punee995/OverWatch-485/SW/src/boards/RAK811BreakBoard/uart-board.h

/*
 / _____)             _              | |
( (____  _____ ____ _| |_ _____  ____| |__
 \____ \| ___ |    (_   _) ___ |/ ___)  _ \
 _____) ) ____| | | || |_| ____( (___| | | |
(______/|_____)_|_|_| \__)_____)\____)_| |_|
    (C)2016 Semtech

Description: Board UART driver implementation

License: Revised BSD License, see LICENSE.TXT file include in the project

Maintainer: Miguel Luis and Gregory Cristian
*/
#ifndef __UART_MCU_H__
#define __UART_MCU_H__

/*!
 * UART peripheral ID
 */
typedef enum
{
    UART_1,
		UART_3,
	  UART_COUNT,
    UART_USB_CDC = 255,
}UartId_t;


int e_getchar(void);
int m_printchar(char ch);
/*!
 * \brief Initializes the UART object and MCU peripheral
 *
 * \param [IN] obj  UART object
 * \param [IN] tx   UART Tx pin name to be used
 * \param [IN] rx   UART Rx pin name to be used
 */
void UartMcuInit( Uart_t *obj, uint8_t uartId, PinNames tx, PinNames rx );

/*!
 * \brief Initializes the UART object and MCU peripheral
 *
 * \param [IN] obj          UART object
 * \param [IN] mode         Mode of operation for the UART
 * \param [IN] baudrate     UART baudrate
 * \param [IN] wordLength   packet length
 * \param [IN] stopBits     stop bits setup
 * \param [IN] parity       packet parity
 * \param [IN] flowCtrl     UART flow control
 */
void UartMcuConfig( Uart_t *obj, UartMode_t mode, uint32_t baudrate, WordLength_t wordLength, StopBits_t stopBits, Parity_t parity, FlowCtrl_t flowCtrl );

/*!
 * \brief DeInitializes the UART object and MCU peripheral
 *
 * \param [IN] obj  UART object
 */
void UartMcuDeInit( Uart_t *obj );

/*!
 * \brief Sends a character to the UART
 *
 * \param [IN] obj   UART object
 * \param [IN] data  Character to be sent
 * \retval status    [0: OK, 1: Busy]
 */
uint8_t UartMcuPutChar( Uart_t *obj, uint8_t data );

/*!
 * \brief Sends a character to the UART
 *
 * \param [IN] obj   UART object
 * \param [IN] data  Characters to be sent
 * \param [IN] size  number of characters to send
 * \retval status    [0: OK, 1: Busy]
 */
uint8_t UartMcuPutBuffer( Uart_t *obj, uint8_t *data, uint16_t size );

/*!
 * \brief Gets a character from the UART
 *
 * \param [IN] obj   UART object
 * \param [IN] data  Received character
 * \retval status    [0: OK, 1: Busy]
 */
uint8_t UartMcuGetChar( Uart_t *obj, uint8_t *data );

/*!
 * \brief Gets a character from the UART (blocking mode)
 *
 * \param [IN] obj   UART object
 * \param [IN] data  Received character
 * \param [IN] size  number of characters to be received
 * \retval status    [0: OK, 1: Busy]
 */
uint8_t UartMcuGetBuffer( Uart_t *obj, uint8_t *data, uint16_t size );


#endif // __UART_MCU_H__
